Addy771/Hex-Cell-Holder/Photos/para_holder.png

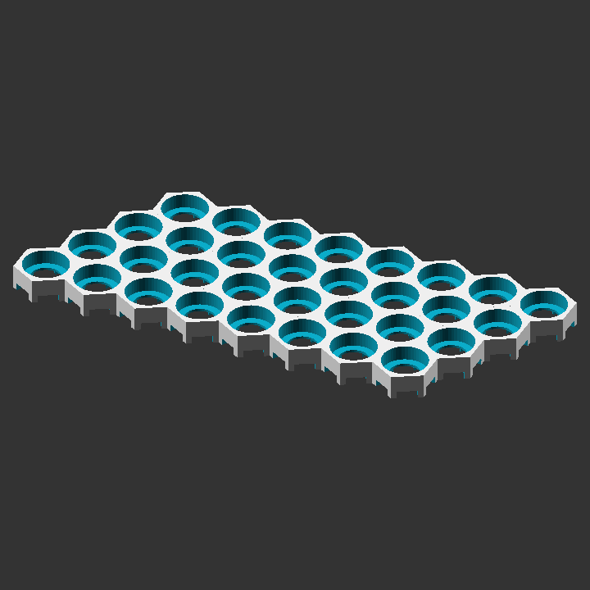
Photos/para_holder.png
