Addy771/Hex-Cell-Holder/Photos/SocoTC Battery/20210601_131000.jpg

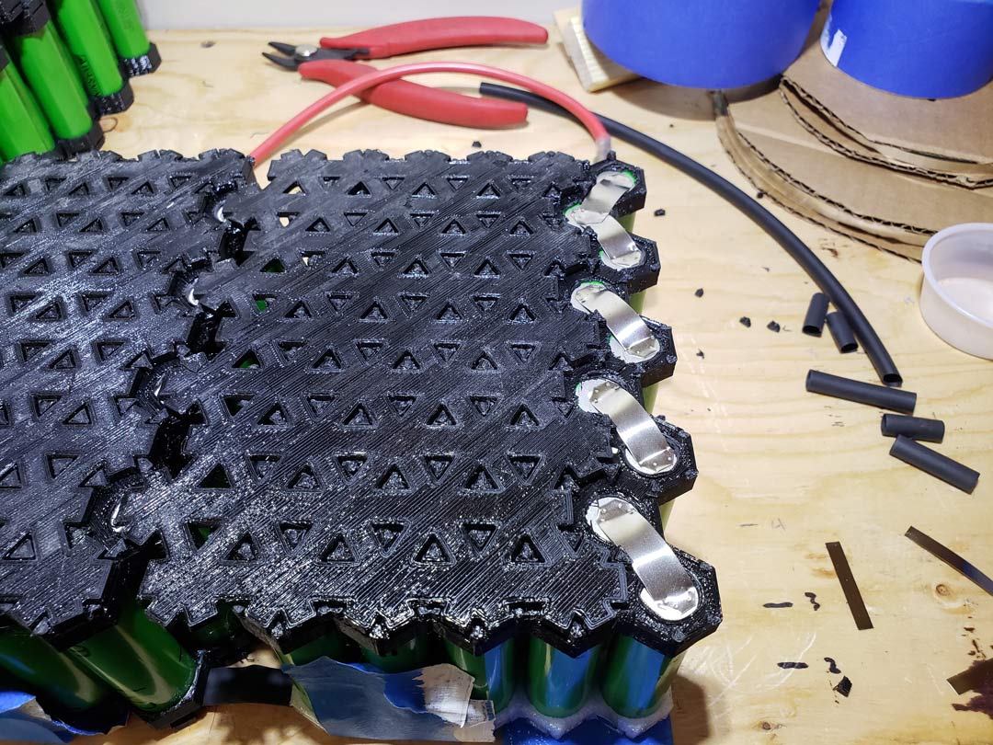
Photos/SocoTC Battery/20210601_131000.jpg
