Addy771/Hex-Cell-Holder/Photos/SocoTC Battery/20210601_131421.jpg

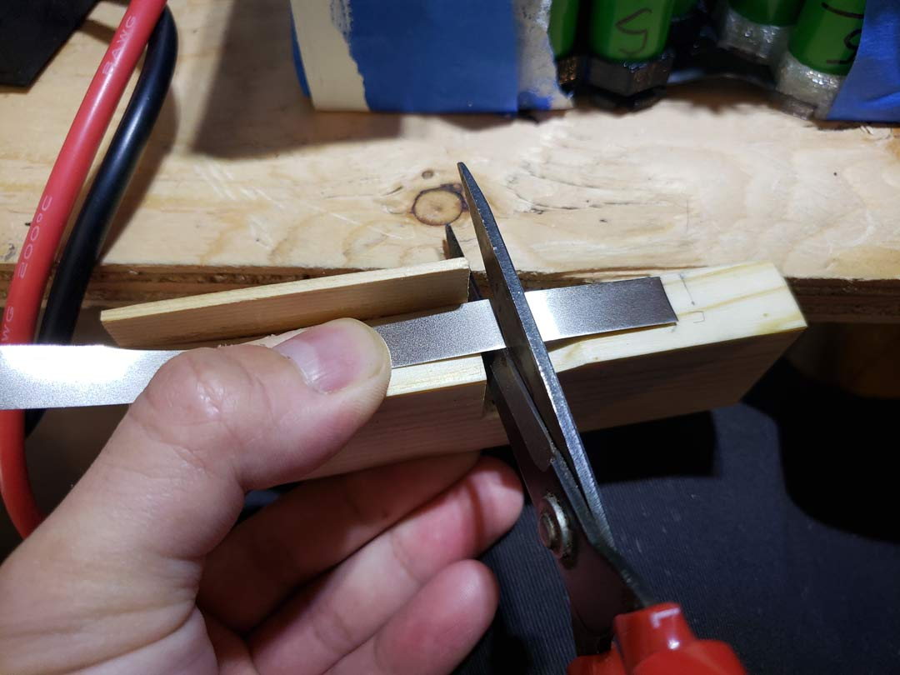
Photos/SocoTC Battery/20210601_131421.jpg
