Addy771/Hex-Cell-Holder/Photos/SocoTC Battery/20210601_133816.jpg

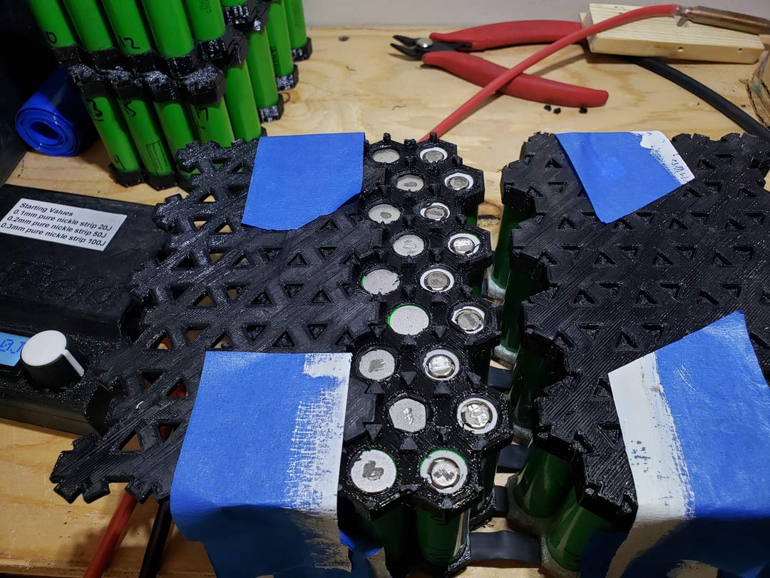
Photos/SocoTC Battery/20210601_133816.jpg
