Addy771/Hex-Cell-Holder/Photos/SocoTC Battery/20210602_152010.jpg

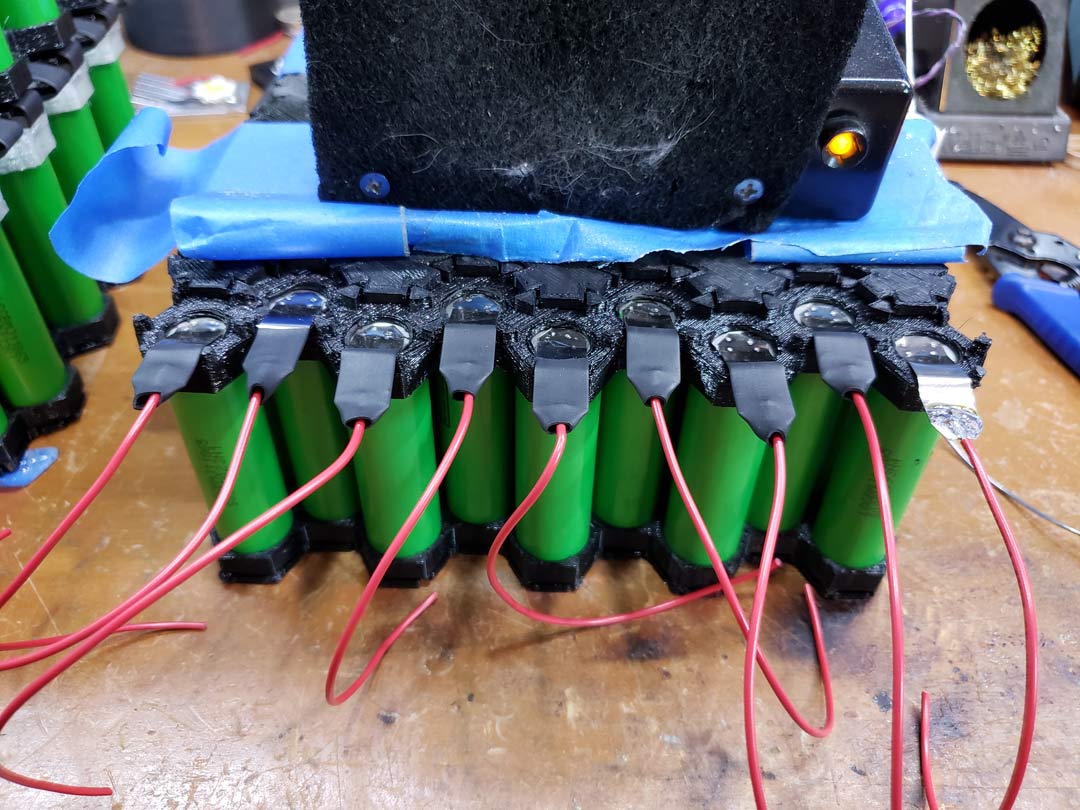
Photos/SocoTC Battery/20210602_152010.jpg
