Addy771/Hex-Cell-Holder/Photos/SocoTC Battery/20210603_125015.jpg

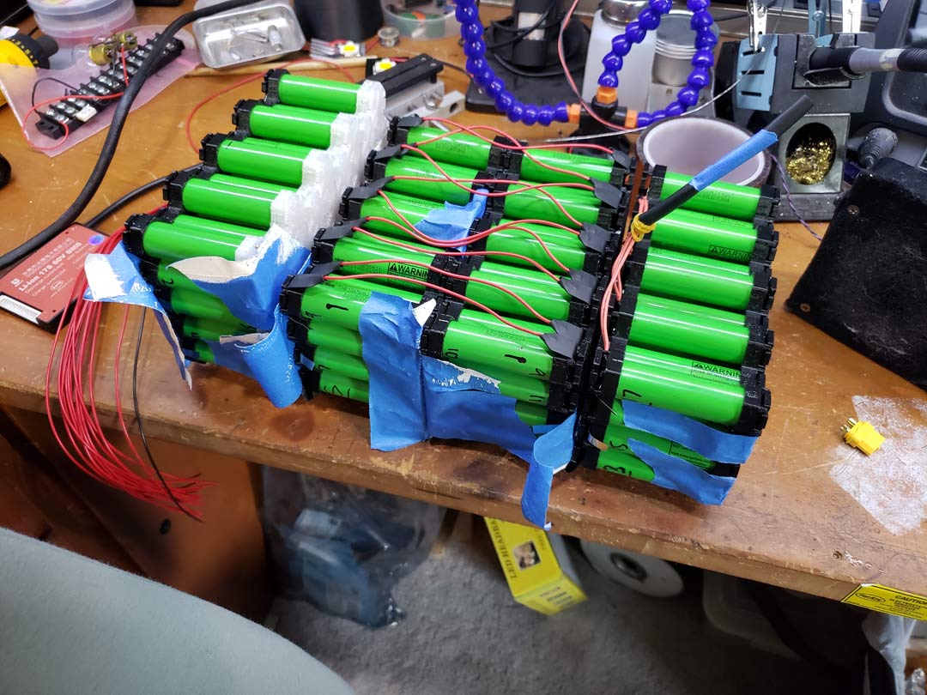
Photos/SocoTC Battery/20210603_125015.jpg
