Addy771/Hex-Cell-Holder/Photos/SocoTC Battery/20210603_140744.jpg

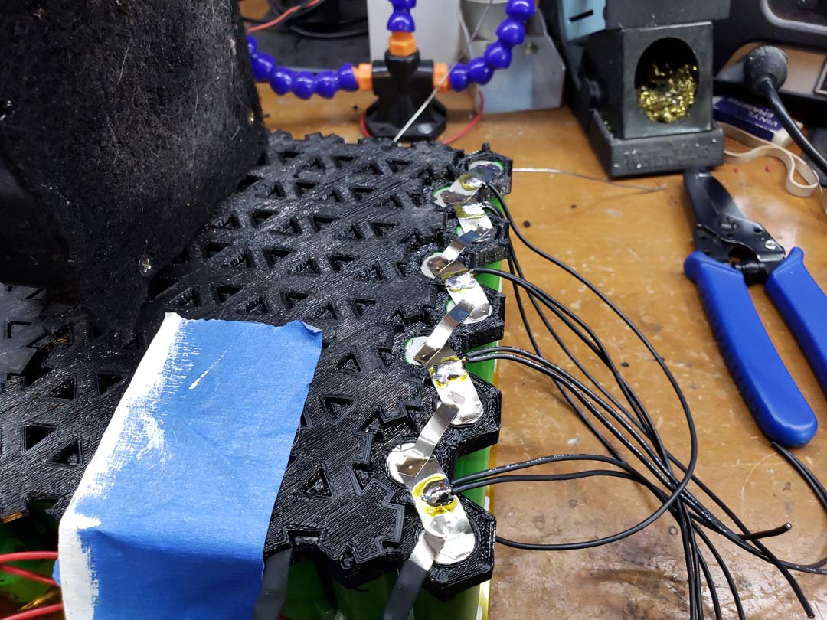
Photos/SocoTC Battery/20210603_140744.jpg
