Addy771/Hex-Cell-Holder/Photos/SocoTC Battery/20210603_144326.jpg

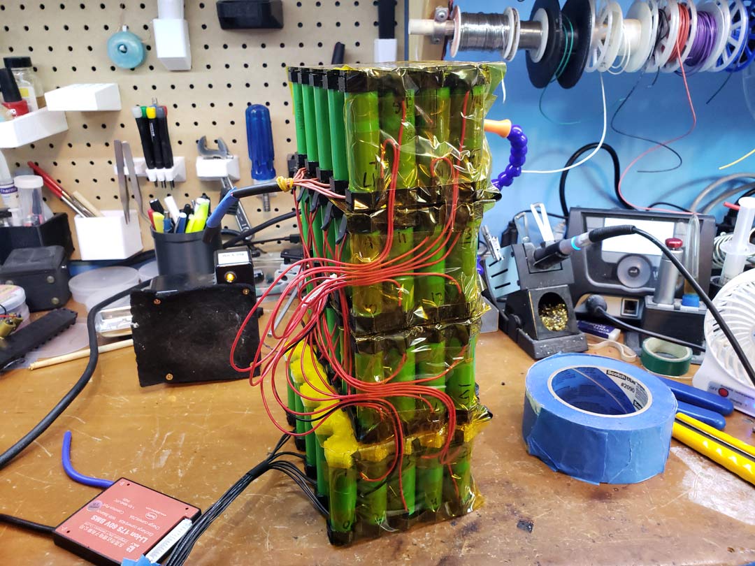
Photos/SocoTC Battery/20210603_144326.jpg
