Addy771/Hex-Cell-Holder/Photos/SocoTC Battery/20210604_145650.jpg

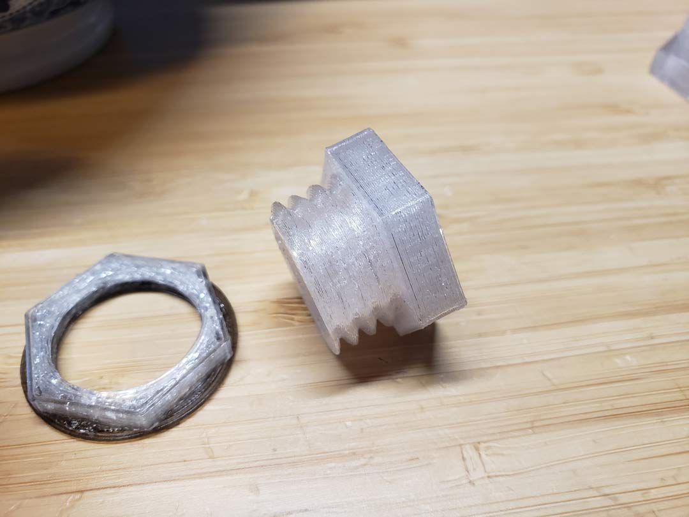
Photos/SocoTC Battery/20210604_145650.jpg
