Addy771/Hex-Cell-Holder/Photos/SocoTC Battery/20210607_144614.jpg

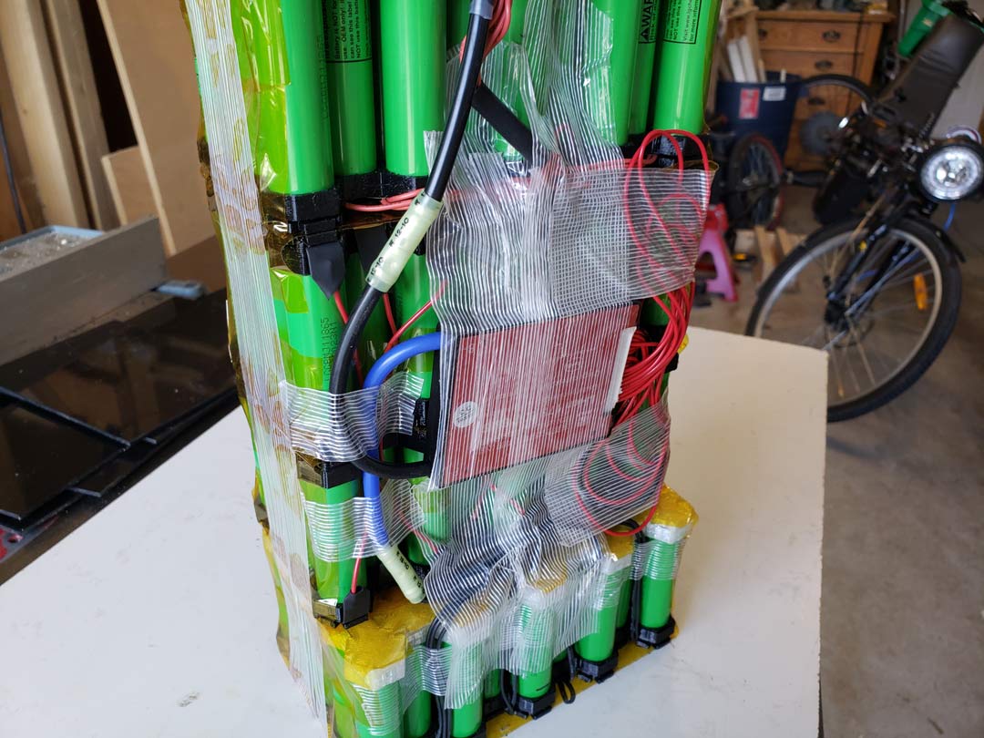
Photos/SocoTC Battery/20210607_144614.jpg
