Addy771/Hex-Cell-Holder/Photos/SocoTC Battery/20210607_145558.jpg

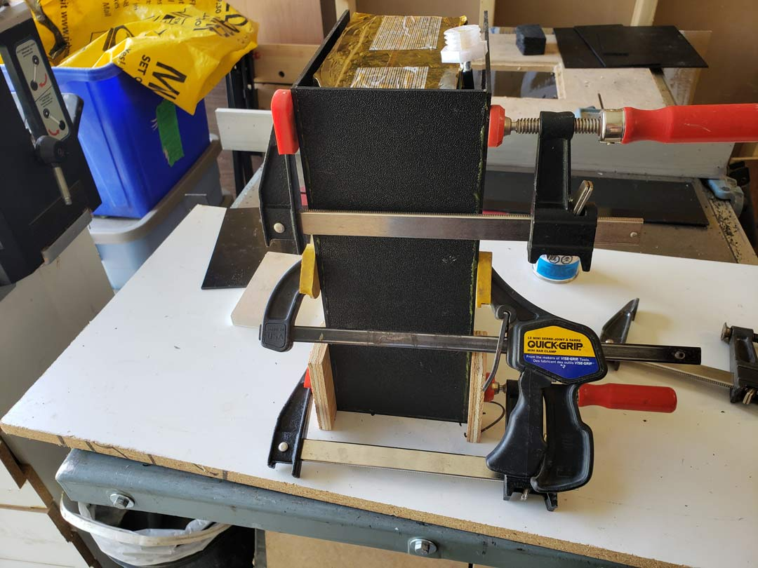
Photos/SocoTC Battery/20210607_145558.jpg
