Addy771/Hex-Cell-Holder/Photos/SocoTC Battery/20210607_153514.jpg

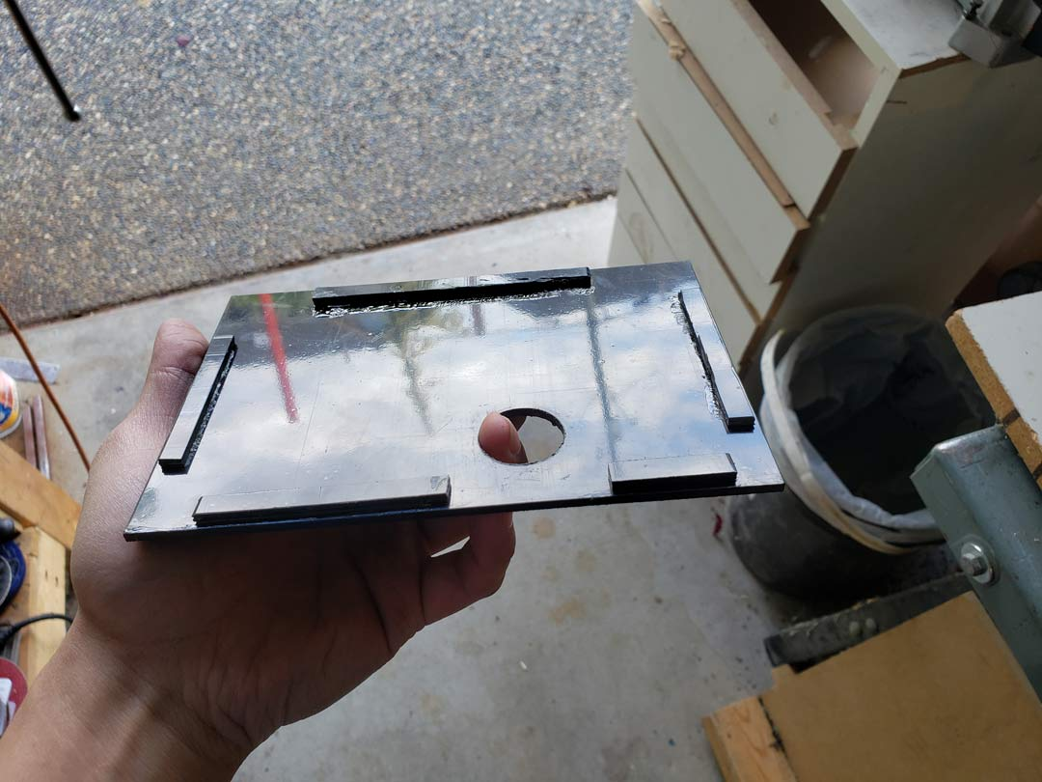
Photos/SocoTC Battery/20210607_153514.jpg
