Addy771/Hex-Cell-Holder/Photos/SocoTC Battery/IMG-20210621-WA0002.jpg

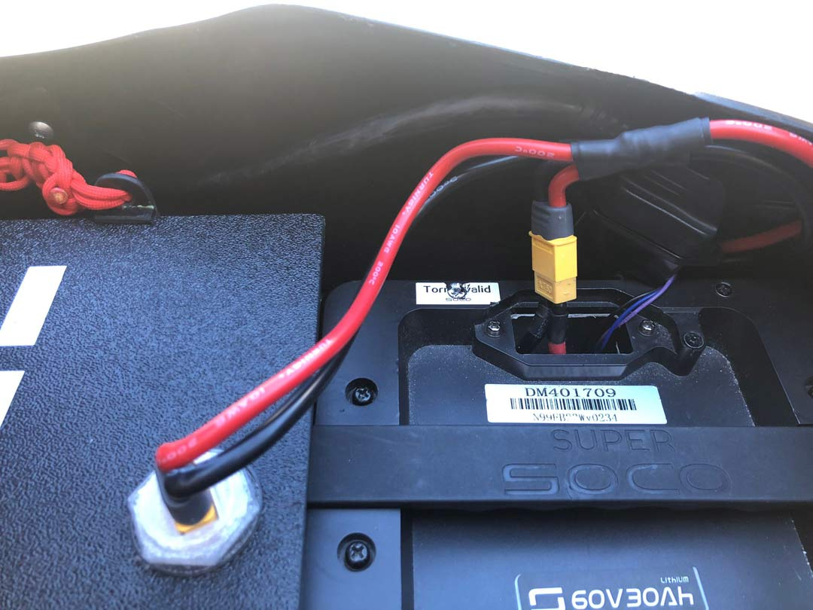
Photos/SocoTC Battery/IMG-20210621-WA0002.jpg
