Addy771/Hex-Cell-Holder/Photos/SocoTC Battery/IMG-20210621-WA0003.jpg

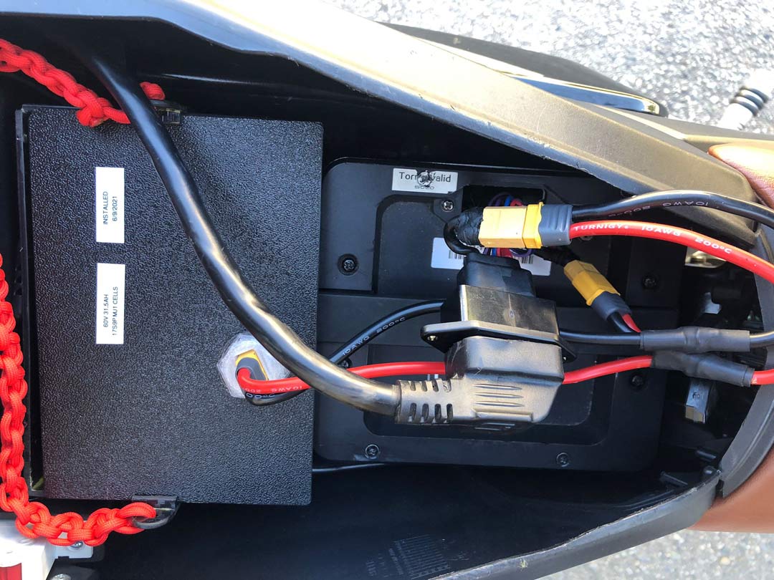
Photos/SocoTC Battery/IMG-20210621-WA0003.jpg
